bribot/AlwaysAvailableWaitingWaiter/Screen/src/driver.h

// This doesn't wotk in platformio because it's dumb and needs to be in the ini file as flags ¯\_(ツ)_/¯
#define BOARD_SCREEN_COMBO 503 // 5.83 inch monochrome ePaper Screen （UC8179）
#define USE_XIAO_EPAPER_DISPLAY_BOARD_EE04
