bribot/AlwaysAvailableWaitingWaiter/Audio/seeedSpeaker/src/eye_emotes.h

static const uint8_t idle_eye[8] PROGMEM = {
    0b00000000,
    0b00000000,
    0b00000000,
    0b01111100,
    0b01111100,
    0b00000000,
    0b00000000,
    0b00000000
};

static const uint8_t leftidle_eye[8] PROGMEM = {
    0b00000000,
    0b00000000,
    0b01111100,
    0b01111100,
    0b00000000,
    0b00000000,
    0b00000000,
    0b00000000
};

static const uint8_t rightidle_eye[8] PROGMEM = {
    0b00000000,
    0b00000000,
    0b00000000,
    0b00000000,
    0b01111100,
    0b01111100,
    0b00000000,
    0b00000000
};

static const uint8_t closed_eye[8] PROGMEM = {
    0b00000000,
    0b00000000,
    0b00000000,
    0b00010000,
    0b00010000,
    0b00000000,
    0b00000000,
    0b00000000
};

static const uint8_t sad_eye[8] PROGMEM = {
    0b00000000,
    0b00011000,
    0b00100000,
    0b00100000,
    0b00100000,
    0b00100000,
    0b00011000,
    0b00000000
};

static const uint8_t happy_face[8] PROGMEM = {
  0b00111100,
  0b01000010,
  0b10100101,
  0b10000001,
  0b10100101,
  0b10011001,
  0b01000010,
  0b00111100
};

static const uint8_t tag_found_bmp[8] PROGMEM = {
  0b00000000,
  0b00000001,
  0b00000010,
  0b00000100,
  0b10001000,
  0b01010000,
  0b00100000,
  0b00000000
};

static const uint8_t error[8] PROGMEM = {
  0b00000000,
  0b01000010,
  0b00100100,
  0b00011000,
  0b00011000,
  0b00100100,
  0b01000010,
  0b00000000,
};

static const uint8_t tag1[8] PROGMEM = {
  0b00000000,
  0b00000000,
  0b00000000,
  0b00000100,
  0b01111110,
  0b00000000,
  0b00000000,
  0b00000000,
};

static const uint8_t tag2[8] PROGMEM = {
  0b00000000,
  0b00000000,
  0b01100010,
  0b01010001,
  0b01001001,
  0b01000110,
  0b00000000,
  0b00000000,
};

static const uint8_t tag3[8] PROGMEM = {
  0b00000000,
  0b00000000,
  0b01001001,
  0b01001001,
  0b01001001,
  0b00110110,
  0b00000000,
  0b00000000
};

static const uint8_t happy1[8] PROGMEM = {
    0b00000000,
    0b00011000,
    0b00001100,
    0b00001100,
    0b00001100,
    0b00001100,
    0b00011000,
    0b00000000
};

static const uint8_t happy2[8] PROGMEM = {
    0b00000000,
    0b00110000,
    0b00011000,
    0b00011000,
    0b00011000,
    0b00011000,
    0b00110000,
    0b00000000
};


static const uint8_t question_eye[8] PROGMEM = {
    0b00000000,
    0b00000110,
    0b00000001,
    0b10110001,
    0b00011001,
    0b00001110,
    0b00000000,
    0b00000000
};

static const uint8_t wait_eye[8] PROGMEM = {
    0b00011100,
    0b00100010,
    0b01000001,
    0b01001101,
    0b01001001,
    0b00100010,
    0b00011100,
    0b00000000
};

static const uint8_t attention_eye[8] PROGMEM = {
    0b00000000,
    0b00000000,
    0b00000000,
    0b11011111,
    0b11011111,
    0b00000000,
    0b00000000,
    0b00000000
};

static const uint8_t blank[8] PROGMEM = {
    0b00000000,
    0b00000000,
    0b00000000,
    0b00000000,
    0b00000000,
    0b00000000,
    0b00000000,
    0b00000000
};

static const uint8_t filled[8] PROGMEM = {
    0b11111111,
    0b11111111,
    0b11111111,
    0b11111111,
    0b11111111,
    0b11111111,
    0b11111111,
    0b11111111,
};
