bribot/AlwaysAvailableWaitingWaiter/Audio/seeedSpeaker/src/board_pins.h

// Define parameters for the LED strip
#define PIN 1            // Pin connected to the RGB LED
#define NUMPIXELS 1      // Number of LEDs
// const int buttonPin = D3;  
// I2SStream out; 
// I2SConfig config;
//  // start I2S
//    Serial.println("starting I2S...");
//   config = out.defaultConfig(TX_MODE);
//   config.copyFrom(info); 
//   // Custom I2S output pins
//   config.pin_bck = 8;
//   config.pin_ws = 7;
//   config.pin_data = 43;
//   config.pin_data_rx = 44;
//   config.is_master = false;
//   out.begin(config);
